BobMcSoapFace/tomodachi/src/firmware/animations.h

#include <stdint.h>
#ifndef ANIMATIONS
#define ANIMATIONS

static const bool SKULLFRAME[1][32][32] = {{{false, false, false, false, false, false, false, false, false, false, false, false, false, false, false, false, false, false, false, false, false, false, false, false, false, false, false, false, false, false, false, false}, {false, false, false, false, false, false, false, false, false, false, false, false, false, true, true, true, true, true, true, false, false, false, false, false, false, false, false, false, false, false, false, false}, {false, false, false, false, false, false, false, false, false, false, true, true, true, false, false, false, false, false, false, true, true, true, false, false, false, false, false, false, false, false, false, false}, {false, false, false, false, false, false, false, false, true, true, false, false, false, false, false, false, false, false, false, false, false, false, true, true, false, false, false, false, false, false, false, false}, {false, false, false, false, false, false, false, true, false, false, false, false, false, false, false, false, false, false, false, false, false, false, false, false, true, false, false, false, false, false, false, false}, {false, false, false, false, false, false, true, false, false, false, false, false, false, false, false, false, false, false, false, false, false, false, false, false, false, true, false, false, false, false, false, false}, {false, false, false, false, false, false, true, false, false, false, false, false, false, false, false, false, false, f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

#endif
